vives-project-xp/RainingLEDs/src/afmetingen.png

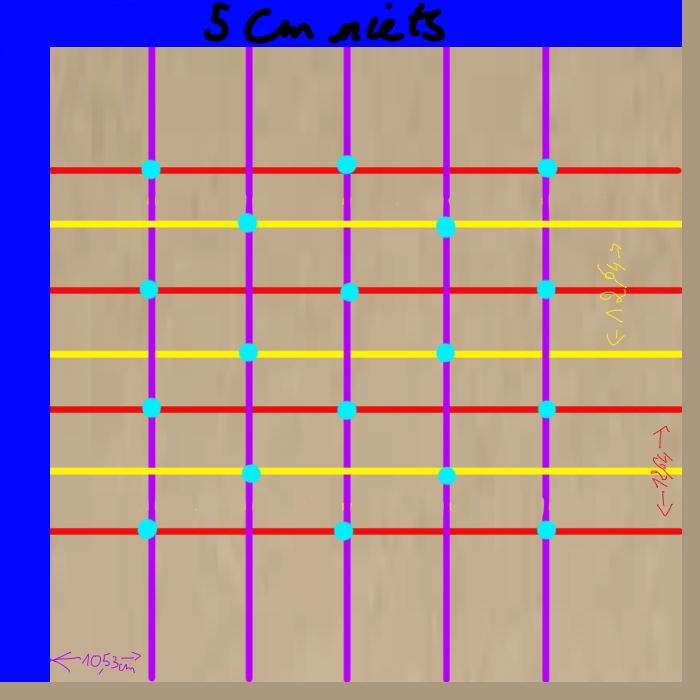
src/afmetingen.png
