vives-project-xp/RainingLEDs/Code/Final code/src/effects.h

#pragma once

// Include libraries
#include <Adafruit_NeoPixel.h>

// Define effects
const String EFFECTS[] = {
  "rainEffect", 
  "waveFade",
  "blinkingStarlight",
  "sunriseEffect",
  "rippleEffect",
  "fire",
  "breathingEffect",
};

// Define delays for each effect
enum Delays {
  fill = 100,
  rainEffect = 100,
  waveFade = 100,
  blinkingStarlight = 100,
  sunrise = 100,
  rainbow = 100,
  rippleEffect = 100,
  other = 100,
};

// Define custom types
struct Color {
  int r;
  int g;
  int b;
  int w;
};

// Function prototypes
void rainEffects(Adafruit_NeoPixel ledstrips[], int num_ledstrips);
void waveFadeEffect(Adafruit_NeoPixel ledstrips[], int num_ledstrips, String color); 
void sunriseEffect(Adafruit_NeoPixel ledstrips[], int num_ledstrips); 
void rainbowEffect(Adafruit_NeoPixel ledstrips[], int num_ledstrips, long &hue); 
void setPixelColorAll(Adafruit_NeoPixel ledstrips[], int num_ledstrips, int pixel, Color color);
void fillAll(Adafruit_NeoPixel ledstrips[], int num_ledstrips, Color color);
void turnOnRandomLEDs(Adafruit_NeoPixel ledstrips[], int numLEDs); 
void blinkingStarlights(Adafruit_NeoPixel ledstrips[], int delayTime); 
void rippleEffects(Adafruit_NeoPixel ledstrips[], int num_ledstrips, Color color); 
void everyOther(Adafruit_NeoPixel ledstrips[], int num_ledstrips, Color color); 
void fireEffect(Adafruit_NeoPixel ledstrips[], int num_ledstrips) ;
void breathingEffect(Adafruit_NeoPixel ledstrips[], int num_ledstrips);
